tor-nky/coconut42/PCB/coconut42.kicad_sch

## KiCad design PCB/coconut42.kicad_sch (2024-08-20, an earlier design)

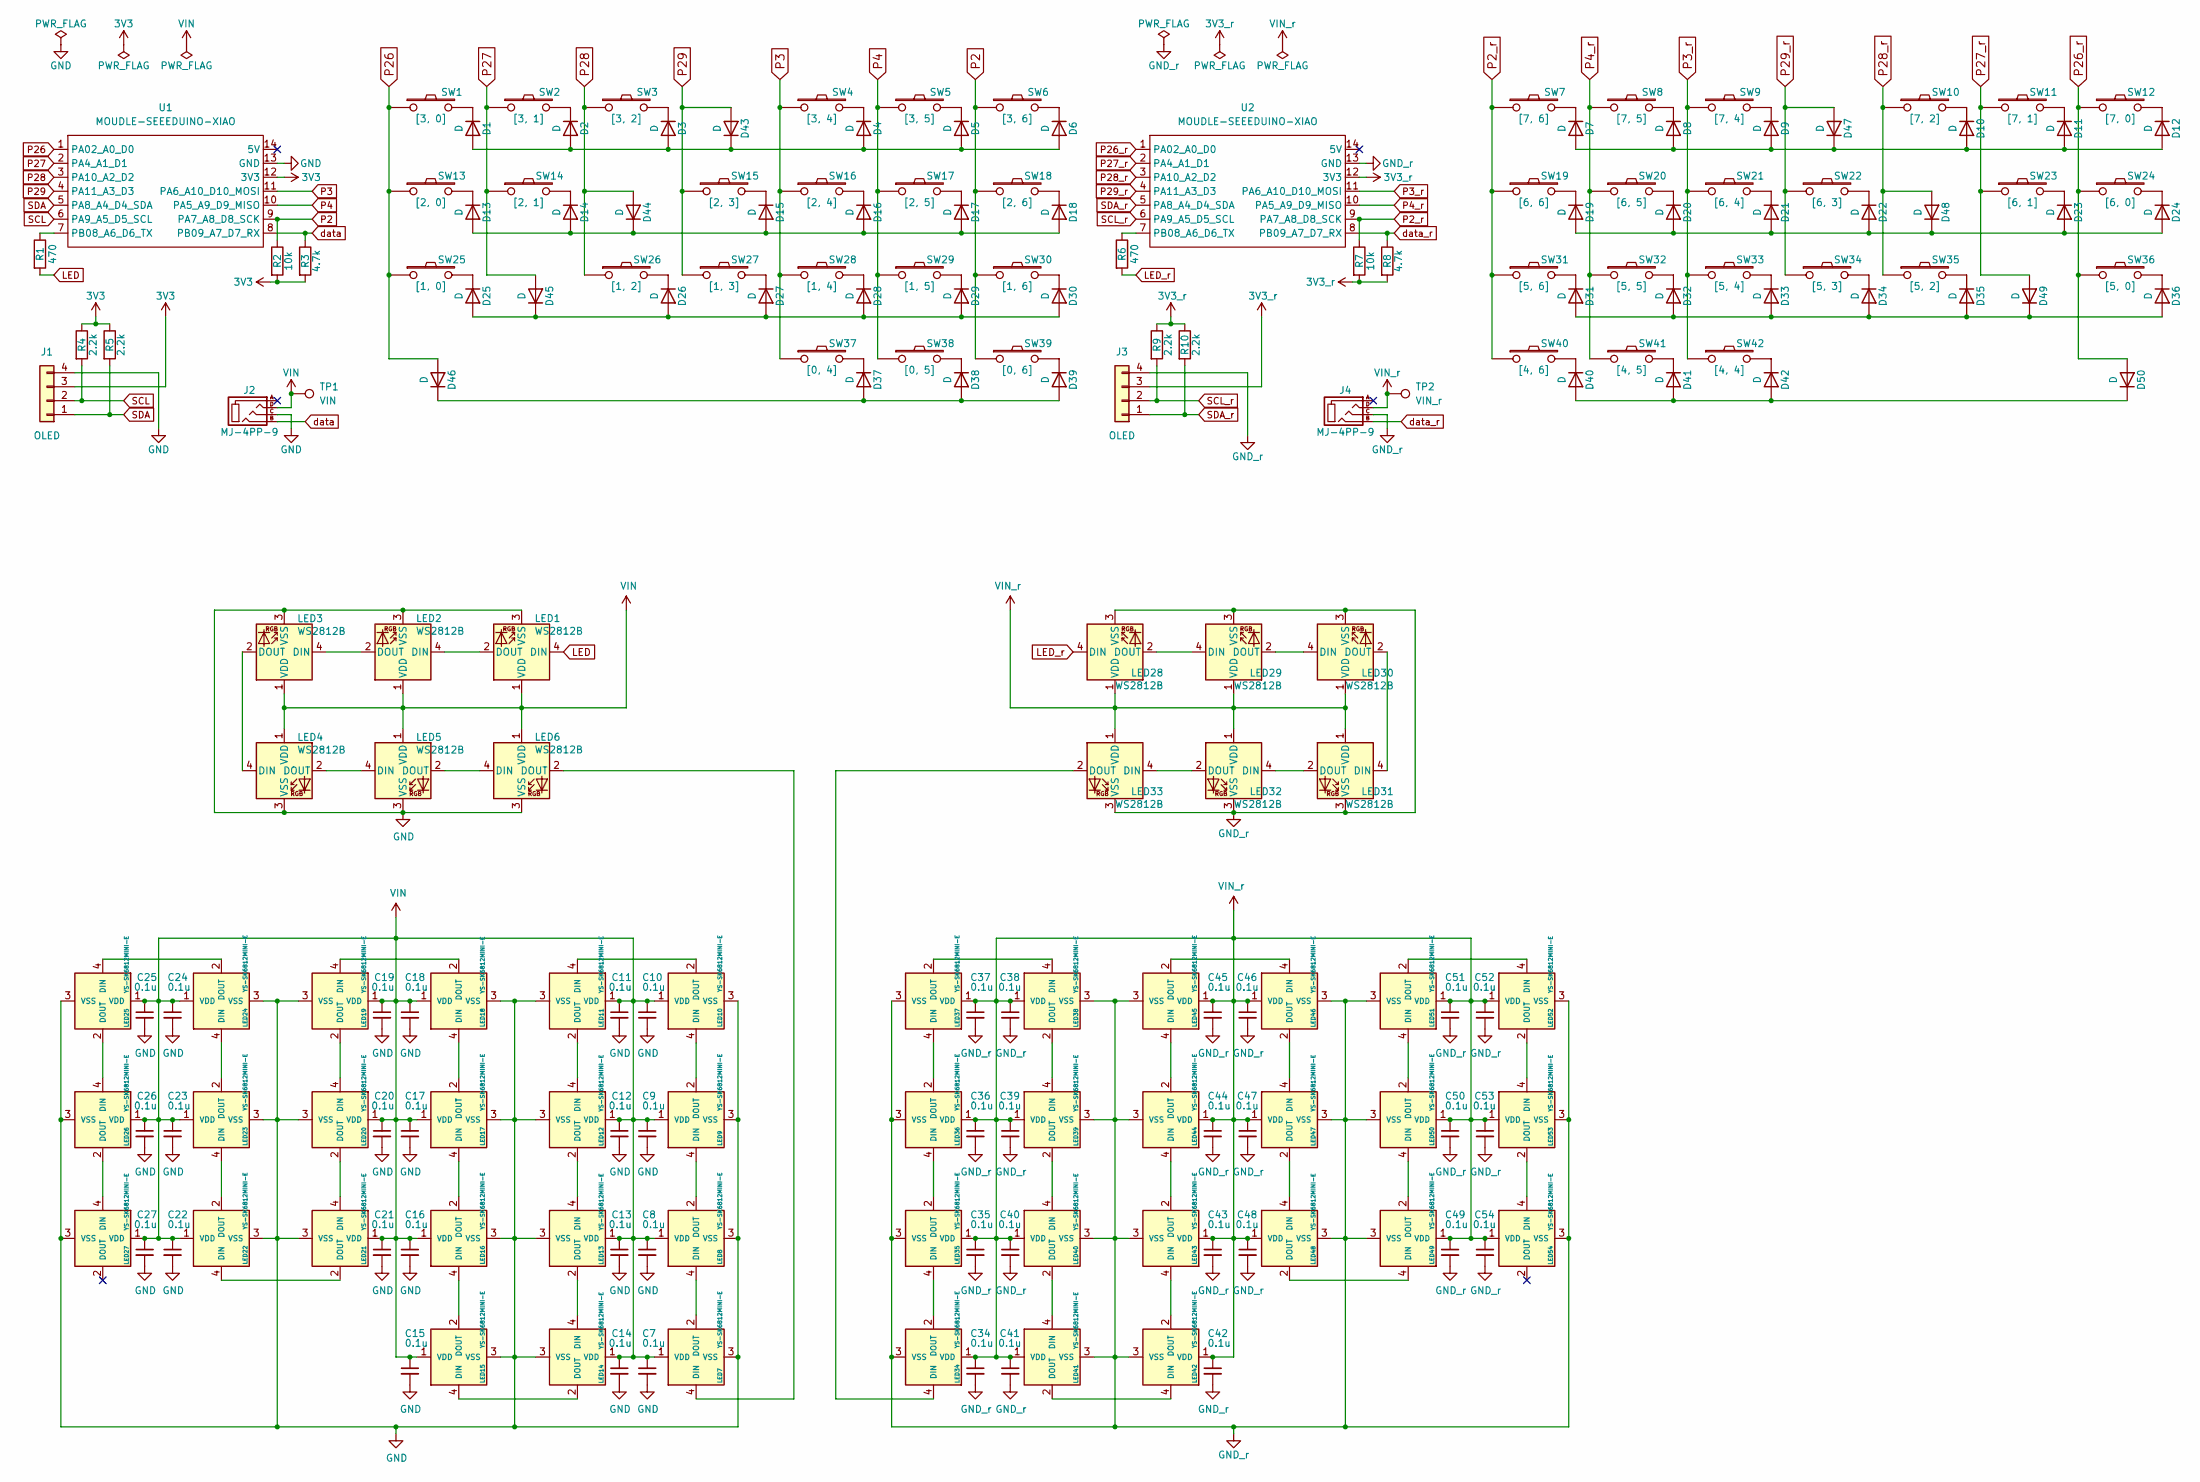
[picture p8: schematic coconut42.kicad_sch]

Parts:
C7, C8, C9, C10, C11, C12, C13, C14, C15, C16, C17, C18, C19, C20, C21, C22, C23, C24, C25, C26, C27, C34, C35, C36, C37, C38, C39, C40, C41, C42, C43, C44, C45, C46, C47, C48, C49, C50, C51, C52, C53, C54: 0.1u; C_0603_1608Metric_Pad1.08x0.95mm_HandSolder
D1, D2, D3, D4, D5, D6, D7, D8, D9, D10, D11, D12, D13, D14, D15, D16, D17, D18, D19, D20, D21, D22, D23, D24, D25, D26, D27, D28, D29, D30, D31, D32, D33, D34, D35, D36, D37, D38, D39, D40, D41, D42, D43, D44, D45, D46, D47, D48, D49, D50: D; D3_SMD_v2
J1, J3: OLED; OLED_1side
J2, J4: MJ-4PP-9; MJ-4PP-9_1side
LED1, LED2: WS2812B; LED_WS2812B_PLCC4_5.0x5.0mm_P3.2mm
LED3, LED4, LED5, LED6, LED28, LED29, LED30, LED31, LED32, LED33: WS2812B; LED_WS2812B-PLCC4
LED7, LED8, LED9, LED10, LED11, LED12, LED13, LED14, LED15, LED16, LED17, LED18, LED19, LED20, LED21, LED22, LED23, LED24, LED25, LED26, LED27, LED34, LED35, LED36, LED37, LED38, LED39, LED40, LED41, LED42, LED43, LED44, LED45, LED46, LED47, LED48, LED49, LED50, LED51, LED52, LED53, LED54: YS-SK6812MINI-E
R1, R6: 470; R
R2, R7: 10k; R
R3, R8: 4.7k; R
R4, R5, R9, R10: 2.2k; R
SW1: [3, 0]; CherryMX_Hotswap
SW2: [3, 1]; CherryMX_Hotswap
SW3: [3, 2]; CherryMX_Hotswap
SW4: [3, 4]; CherryMX_Hotswap
SW5: [3, 5]; CherryMX_Hotswap
SW6: [3, 6]; CherryMX_Hotswap
SW7: [7, 6]; CherryMX_Hotswap
SW8: [7, 5]; CherryMX_Hotswap
SW9: [7, 4]; CherryMX_Hotswap
SW10: [7, 2]; CherryMX_Hotswap
SW11: [7, 1]; CherryMX_Hotswap
SW12: [7, 0]; CherryMX_Hotswap
SW13: [2, 0]; CherryMX_Hotswap
SW14: [2, 1]; CherryMX_Hotswap
SW15: [2, 3]; CherryMX_Hotswap
SW16: [2, 4]; CherryMX_Hotswap
SW17: [2, 5]; CherryMX_Hotswap
SW18: [2, 6]; CherryMX_Hotswap
SW19: [6, 6]; CherryMX_Hotswap
SW20: [6, 5]; CherryMX_Hotswap
SW21: [6, 4]; CherryMX_Hotswap
SW22: [6, 3]; CherryMX_Hotswap
SW23: [6, 1]; CherryMX_Hotswap
SW24: [6, 0]; CherryMX_Hotswap
SW25: [1, 0]; CherryMX_Hotswap
SW26: [1, 2]; CherryMX_Hotswap
SW27: [1, 3]; CherryMX_Hotswap
SW28: [1, 4]; CherryMX_Hotswap
SW29: [1, 5]; CherryMX_Hotswap
SW30: [1, 6]; CherryMX_Hotswap
SW31: [5, 6]; CherryMX_Hotswap
SW32: [5, 5]; CherryMX_Hotswap
SW33: [5, 4]; CherryMX_Hotswap
SW34: [5, 3]; CherryMX_Hotswap
SW35: [5, 2]; CherryMX_Hotswap
SW36: [5, 0]; CherryMX_Hotswap
SW37: [0, 4]; CherryMX_Hotswap
SW38: [0, 5]; CherryMX_Hotswap
SW39: [0, 6]; CherryMX_Hotswap
SW40: [4, 6]; CherryMX_Hotswap
SW41: [4, 5]; CherryMX_Hotswap
SW42: [4, 4]; CherryMX_Hotswap
TP1: VIN; TestPoint_THTPad_1.6x1.6mm_Drill0.8mm
TP2: VIN_r; TestPoint_THTPad_1.6x1.6mm_Drill0.8mm
U1, U2: MOUDLE-SEEEDUINO-XIAO

Connections:
3V3: J1.3, R2.2, R3.2, R4.1, R5.1, U1.12 (3V3)
3V3_r: J3.3, R7.2, R8.2, R9.1, R10.1, U2.12 (3V3)
GND: C7.2, C8.2, C9.2, C10.2, C11.2, C12.2, C13.2, C14.2, C15.2, C16.2, C17.2, C18.2, C19.2, C20.2, C21.2, C22.2, C23.2, C24.2, C25.2, C26.2, C27.2, J1.4, J2.C, LED1.3 (VSS), LED2.3 (VSS), LED3.3 (VSS), LED4.3 (VSS), LED5.3 (VSS), LED6.3 (VSS), LED7.3 (VSS), LED8.3 (VSS), LED9.3 (VSS), LED10.3 (VSS), LED11.3 (VSS), LED12.3 (VSS), LED13.3 (VSS), LED14.3 (VSS), LED15.3 (VSS), LED16.3 (VSS), LED17.3 (VSS), LED18.3 (VSS), LED19.3 (VSS), LED20.3 (VSS), LED21.3 (VSS), LED22.3 (VSS), LED23.3 (VSS), LED24.3 (VSS), LED25.3 (VSS), LED26.3 (VSS), LED27.3 (VSS), U1.13 (GND)
GND_r: C34.2, C35.2, C36.2, C37.2, C38.2, C39.2, C40.2, C41.2, C42.2, C43.2, C44.2, C45.2, C46.2, C47.2, C48.2, C49.2, C50.2, C51.2, C52.2, C53.2, C54.2, J3.4, J4.C, LED28.3 (VSS), LED29.3 (VSS), LED30.3 (VSS), LED31.3 (VSS), LED32.3 (VSS), LED33.3 (VSS), LED34.3 (VSS), LED35.3 (VSS), LED36.3 (VSS), LED37.3 (VSS), LED38.3 (VSS), LED39.3 (VSS), LED40.3 (VSS), LED41.3 (VSS), LED42.3 (VSS), LED43.3 (VSS), LED44.3 (VSS), LED45.3 (VSS), LED46.3 (VSS), LED47.3 (VSS), LED48.3 (VSS), LED49.3 (VSS), LED50.3 (VSS), LED51.3 (VSS), LED52.3 (VSS), LED53.3 (VSS), LED54.3 (VSS), U2.13 (GND)
LED: LED1.4 (DIN), R1.2
LED_r: LED28.4 (DIN), R6.2
unnamed: D1.1 (K), SW1.2
unnamed: D1.2 (A), D2.2 (A), D3.2 (A), D4.2 (A), D5.2 (A), D6.2 (A), D43.1 (K)
unnamed: D2.1 (K), SW2.2
unnamed: D3.1 (K), SW3.2
unnamed: D4.1 (K), SW4.2
unnamed: D5.1 (K), SW5.2
unnamed: D6.1 (K), SW6.2
unnamed: D7.1 (K), SW7.2
unnamed: D8.1 (K), SW8.2
unnamed: D9.1 (K), SW9.2
unnamed: D10.1 (K), SW10.2
unnamed: D7.2 (A), D8.2 (A), D9.2 (A), D10.2 (A), D11.2 (A), D12.2 (A), D47.1 (K)
unnamed: D11.1 (K), SW11.2
unnamed: D12.1 (K), SW12.2
unnamed: D13.1 (K), SW13.2
unnamed: D13.2 (A), D14.2 (A), D15.2 (A), D16.2 (A), D17.2 (A), D18.2 (A), D44.1 (K)
unnamed: D14.1 (K), SW14.2
unnamed: D15.1 (K), SW15.2
unnamed: D16.1 (K), SW16.2
unnamed: D17.1 (K), SW17.2
unnamed: D18.1 (K), SW18.2
unnamed: D19.1 (K), SW19.2
unnamed: D19.2 (A), D20.2 (A), D21.2 (A), D22.2 (A), D23.2 (A), D24.2 (A), D48.1 (K)
unnamed: D20.1 (K), SW20.2
unnamed: D21.1 (K), SW21.2
unnamed: D22.1 (K), SW22.2
unnamed: D23.1 (K), SW23.2
unnamed: D24.1 (K), SW24.2
unnamed: D25.1 (K), SW25.2
unnamed: D25.2 (A), D26.2 (A), D27.2 (A), D28.2 (A), D29.2 (A), D30.2 (A), D45.1 (K)
unnamed: D26.1 (K), SW26.2
unnamed: D27.1 (K), SW27.2
unnamed: D28.1 (K), SW28.2
unnamed: D29.1 (K), SW29.2
unnamed: D30.1 (K), SW30.2
unnamed: D31.1 (K), SW31.2
unnamed: D31.2 (A), D32.2 (A), D33.2 (A), D34.2 (A), D35.2 (A), D36.2 (A), D49.1 (K)
unnamed: D32.1 (K), SW32.2
unnamed: D33.1 (K), SW33.2
unnamed: D34.1 (K), SW34.2
unnamed: D35.1 (K), SW35.2
unnamed: D36.1 (K), SW36.2
unnamed: D37.1 (K), SW37.2
unnamed: D37.2 (A), D38.2 (A), D39.2 (A), D46.1 (K)
unnamed: D38.1 (K), SW38.2
unnamed: D39.1 (K), SW39.2
unnamed: D40.1 (K), SW40.2
unnamed: D40.2 (A), D41.2 (A), D42.2 (A), D50.1 (K)
unnamed: D41.1 (K), SW41.2
unnamed: D42.1 (K), SW42.2
unnamed: LED1.2 (DOUT), LED2.4 (DIN)
unnamed: LED2.2 (DOUT), LED3.4 (DIN)
unnamed: LED3.2 (DOUT), LED4.4 (DIN)
unnamed: LED4.2 (DOUT), LED5.4 (DIN)
unnamed: LED5.2 (DOUT), LED6.4 (DIN)
unnamed: LED6.2 (DOUT), LED7.4 (DIN)
unnamed: LED7.2 (DOUT), LED8.4 (DIN)
unnamed: LED8.2 (DOUT), LED9.4 (DIN)
unnamed: LED10.2 (DOUT), LED11.4 (DIN)
unnamed: LED9.2 (DOUT), LED10.4 (DIN)
unnamed: LED11.2 (DOUT), LED12.4 (DIN)
unnamed: LED12.2 (DOUT), LED13.4 (DIN)
unnamed: LED13.2 (DOUT), LED14.4 (DIN)
unnamed: LED14.2 (DOUT), LED15.4 (DIN)
unnamed: LED15.2 (DOUT), LED16.4 (DIN)
unnamed: LED16.2 (DOUT), LED17.4 (DIN)
unnamed: LED17.2 (DOUT), LED18.4 (DIN)
unnamed: LED18.2 (DOUT), LED19.4 (DIN)
unnamed: LED19.2 (DOUT), LED20.4 (DIN)
unnamed: LED20.2 (DOUT), LED21.4 (DIN)
unnamed: LED21.2 (DOUT), LED22.4 (DIN)
unnamed: LED22.2 (DOUT), LED23.4 (DIN)
unnamed: LED23.2 (DOUT), LED24.4 (DIN)
unnamed: LED24.2 (DOUT), LED25.4 (DIN)
unnamed: LED25.2 (DOUT), LED26.4 (DIN)
unnamed: LED26.2 (DOUT), LED27.4 (DIN)
unnamed: LED28.2 (DOUT), LED29.4 (DIN)
unnamed: LED29.2 (DOUT), LED30.4 (DIN)
unnamed: LED30.2 (DOUT), LED31.4 (DIN)
unnamed: LED31.2 (DOUT), LED32.4 (DIN)
unnamed: LED32.2 (DOUT), LED33.4 (DIN)
unnamed: LED33.2 (DOUT), LED34.4 (DIN)
unnamed: LED34.2 (DOUT), LED35.4 (DIN)
unnamed: LED35.2 (DOUT), LED36.4 (DIN)
unnamed: LED36.2 (DOUT), LED37.4 (DIN)
unnamed: LED37.2 (DOUT), LED38.4 (DIN)
unnamed: LED38.2 (DOUT), LED39.4 (DIN)
unnamed: LED39.2 (DOUT), LED40.4 (DIN)
unnamed: LED40.2 (DOUT), LED41.4 (DIN)
unnamed: LED41.2 (DOUT), LED42.4 (DIN)
unnamed: LED42.2 (DOUT), LED43.4 (DIN)
unnamed: LED43.2 (DOUT), LED44.4 (DIN)
unnamed: LED44.2 (DOUT), LED45.4 (DIN)
unnamed: LED45.2 (DOUT), LED46.4 (DIN)
unnamed: LED46.2 (DOUT), LED47.4 (DIN)
unnamed: LED47.2 (DOUT), LED48.4 (DIN)
unnamed: LED48.2 (DOUT), LED49.4 (DIN)
unnamed: LED49.2 (DOUT), LED50.4 (DIN)
unnamed: LED50.2 (DOUT), LED51.4 (DIN)
unnamed: LED51.2 (DOUT), LED52.4 (DIN)
unnamed: LED52.2 (DOUT), LED53.4 (DIN)
unnamed: LED53.2 (DOUT), LED54.4 (DIN)
unnamed: R1.1, U1.7 (PB08_A6_D6_TX)
unnamed: R6.1, U2.7 (PB08_A6_D6_TX)
P2: R2.1, SW6.1, SW18.1, SW30.1, SW39.1, U1.9 (PA7_A8_D8_SCK)
P2_r: R7.1, SW7.1, SW19.1, SW31.1, SW40.1, U2.9 (PA7_A8_D8_SCK)
P3: SW4.1, SW16.1, SW28.1, SW37.1, U1.11 (PA6_A10_D10_MOSI)
P3_r: SW9.1, SW21.1, SW33.1, SW42.1, U2.11 (PA6_A10_D10_MOSI)
P4: SW5.1, SW17.1, SW29.1, SW38.1, U1.10 (PA5_A9_D9_MISO)
P4_r: SW8.1, SW20.1, SW32.1, SW41.1, U2.10 (PA5_A9_D9_MISO)
P26: D46.2 (A), SW1.1, SW13.1, SW25.1, U1.1 (PA02_A0_D0)
P26_r: D50.2 (A), SW12.1, SW24.1, SW36.1, U2.1 (PA02_A0_D0)
P27: D45.2 (A), SW2.1, SW14.1, U1.2 (PA4_A1_D1)
P27_r: D49.2 (A), SW11.1, SW23.1, U2.2 (PA4_A1_D1)
P28: D44.2 (A), SW3.1, SW26.1, U1.3 (PA10_A2_D2)
P28_r: D48.2 (A), SW10.1, SW35.1, U2.3 (PA10_A2_D2)
P29: D43.2 (A), SW15.1, SW27.1, U1.4 (PA11_A3_D3)
P29_r: D47.2 (A), SW22.1, SW34.1, U2.4 (PA11_A3_D3)
SCL: J1.2, R4.2, U1.6 (PA9_A5_D5_SCL)
SCL_r: J3.2, R9.2, U2.6 (PA9_A5_D5_SCL)
SDA: J1.1, R5.2, U1.5 (PA8_A4_D4_SDA)
SDA_r: J3.1, R10.2, U2.5 (PA8_A4_D4_SDA)
VIN: C7.1, C8.1, C9.1, C10.1, C11.1, C12.1, C13.1, C14.1, C15.1, C16.1, C17.1, C18.1, C19.1, C20.1, C21.1, C22.1, C23.1, C24.1, C25.1, C26.1, C27.1, J2.D, LED1.1 (VDD), LED2.1 (VDD), LED3.1 (VDD), LED4.1 (VDD), LED5.1 (VDD), LED6.1 (VDD), LED7.1 (VDD), LED8.1 (VDD), LED9.1 (VDD), LED10.1 (VDD), LED11.1 (VDD), LED12.1 (VDD), LED13.1 (VDD), LED14.1 (VDD), LED15.1 (VDD), LED16.1 (VDD), LED17.1 (VDD), LED18.1 (VDD), LED19.1 (VDD), LED20.1 (VDD), LED21.1 (VDD), LED22.1 (VDD), LED23.1 (VDD), LED24.1 (VDD), LED25.1 (VDD), LED26.1 (VDD), LED27.1 (VDD), TP1.1
VIN_r: C34.1, C35.1, C36.1, C37.1, C38.1, C39.1, C40.1, C41.1, C42.1, C43.1, C44.1, C45.1, C46.1, C47.1, C48.1, C49.1, C50.1, C51.1, C52.1, C53.1, C54.1, J4.D, LED28.1 (VDD), LED29.1 (VDD), LED30.1 (VDD), LED31.1 (VDD), LED32.1 (VDD), LED33.1 (VDD), LED34.1 (VDD), LED35.1 (VDD), LED36.1 (VDD), LED37.1 (VDD), LED38.1 (VDD), LED39.1 (VDD), LED40.1 (VDD), LED41.1 (VDD), LED42.1 (VDD), LED43.1 (VDD), LED44.1 (VDD), LED45.1 (VDD), LED46.1 (VDD), LED47.1 (VDD), LED48.1 (VDD), LED49.1 (VDD), LED50.1 (VDD), LED51.1 (VDD), LED52.1 (VDD), LED53.1 (VDD), LED54.1 (VDD), TP2.1
data: J2.B, R3.1, U1.8 (PB09_A7_D7_RX)
data_r: J4.B, R8.1, U2.8 (PB09_A7_D7_RX)
