tor-nky/coconut42/images/IMG_0215.jpeg

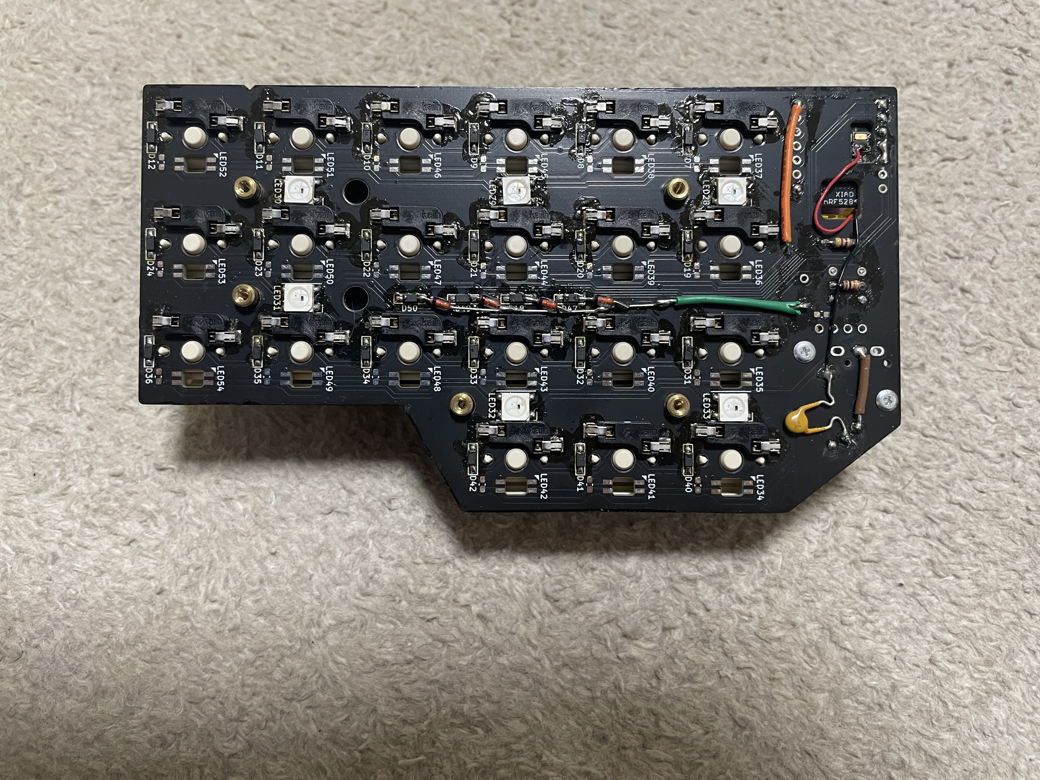
images/IMG_0215.jpeg
