tor-nky/coconut42/images/IMG_0218.jpeg

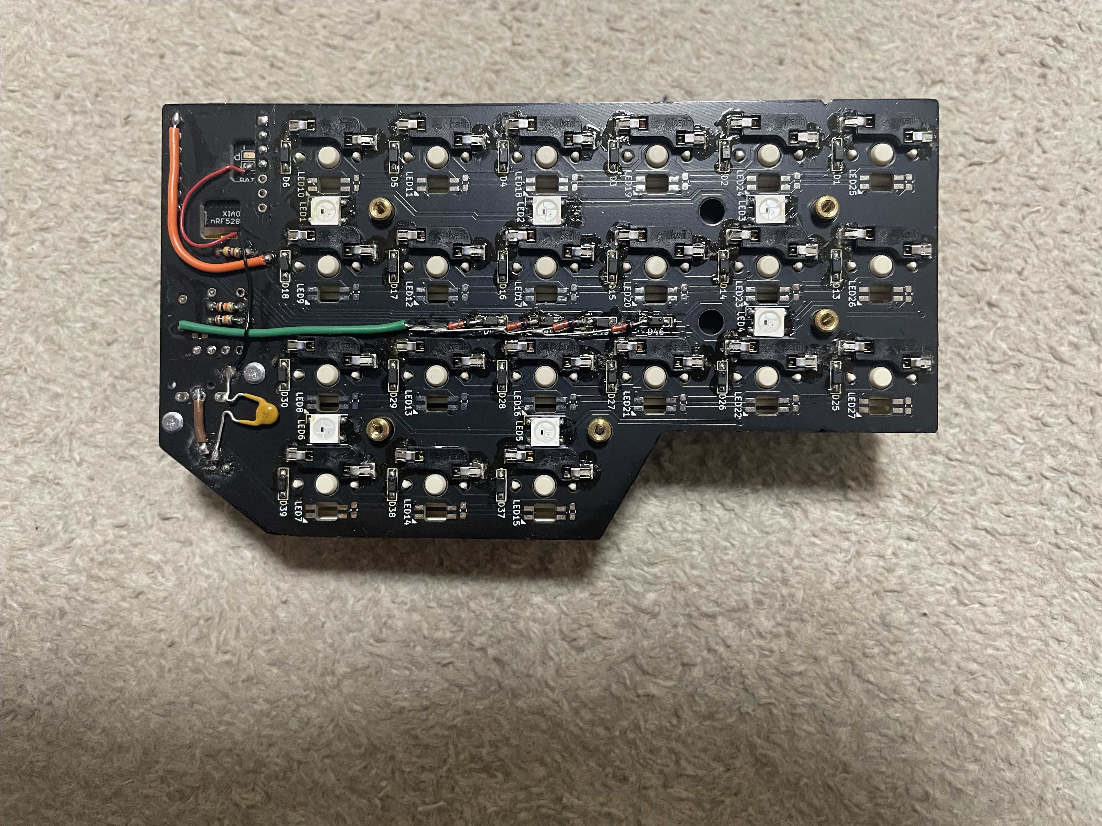
images/IMG_0218.jpeg
